MKme/face-shield/Photos/5.jpg

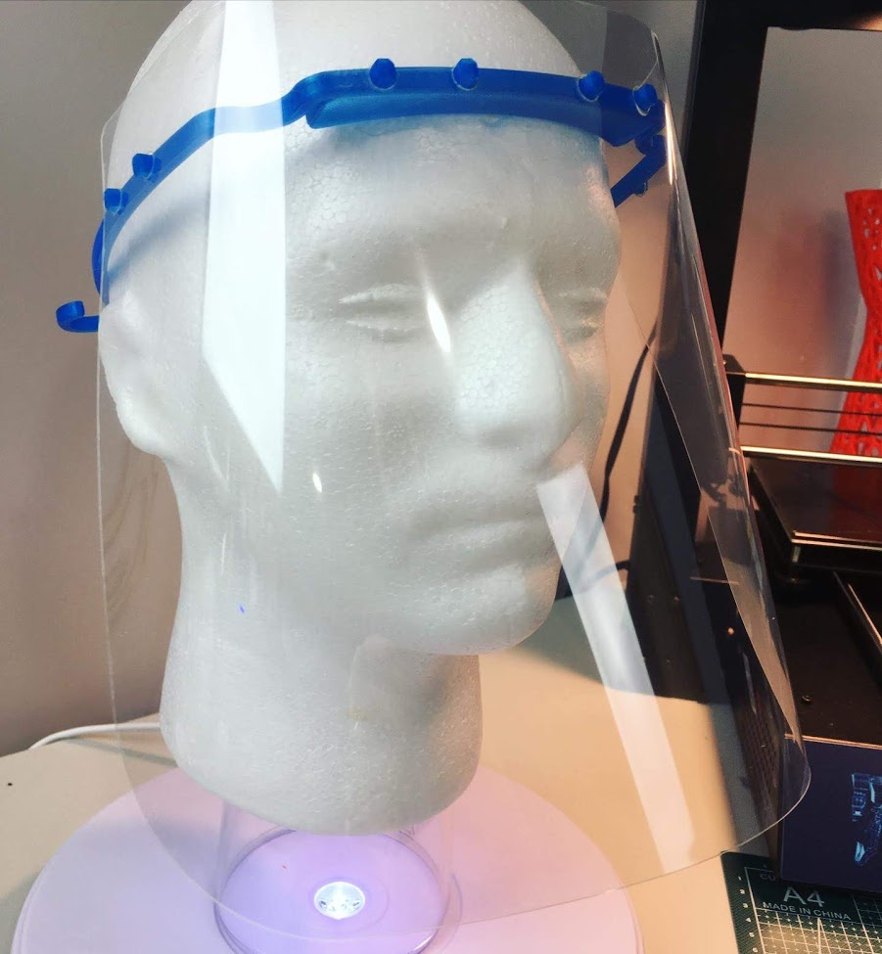
Photos/5.jpg
