MKme/face-shield/Photos/IMG_2852.JPG

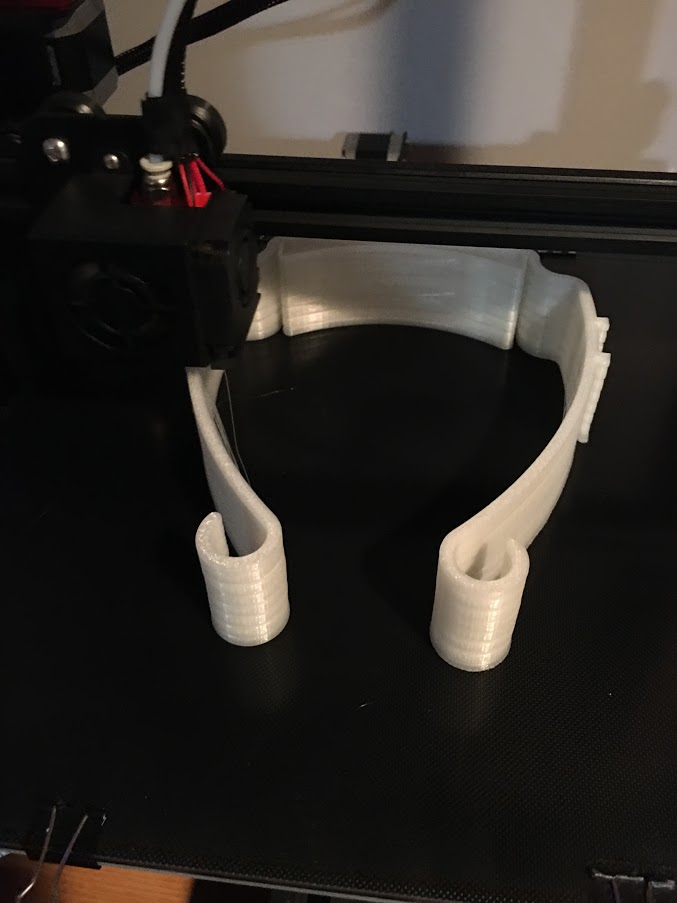
Photos/IMG_2852.JPG
