MKme/face-shield/Photos/1.JPG

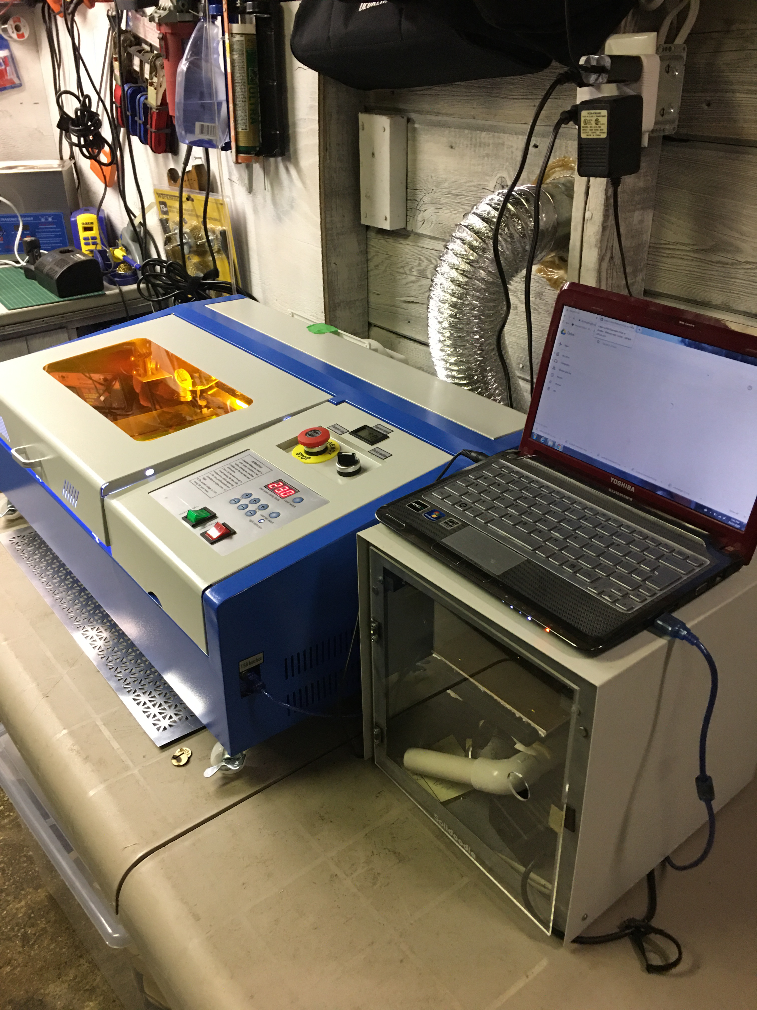
Photos/1.JPG
